boscoverysat/bsat.sat.electronica_de_abordo/pcb/receptor_rf_430mhz/pdf/Receptor RF - SCH.pdf

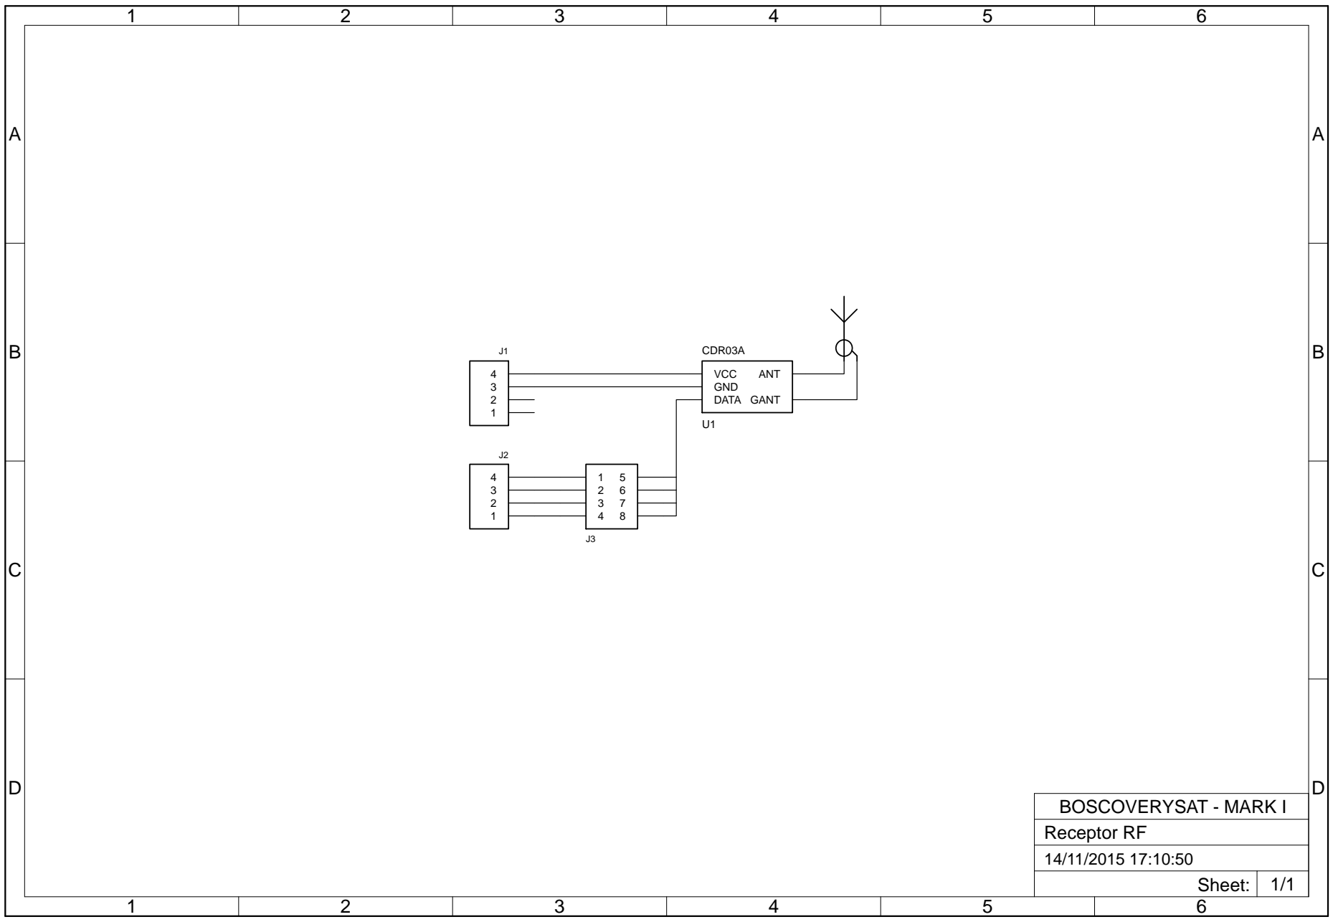
[picture p2: figure]
CDR03A; VCC; DATA; GND; ANT; GANT; Receptor RF; Sheet: 1/1; BOSCOVERYSAT - MARK I
