boscoverysat/bsat.sat.electronica_de_abordo/pcb/receptor_rf_430mhz/pdf/Receptor RF - PCB.pdf

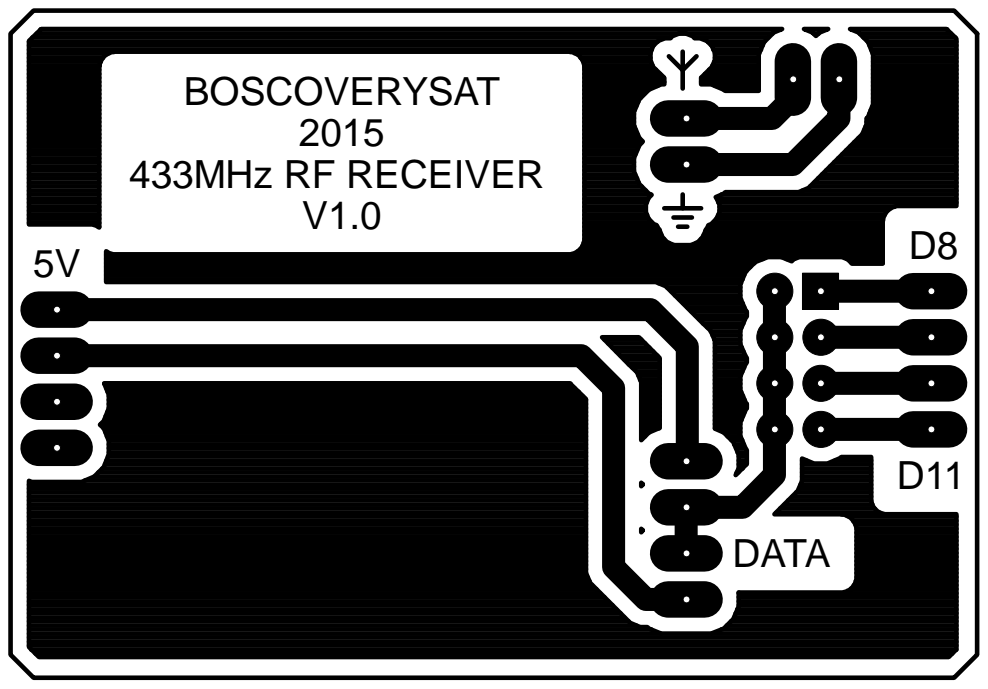
[picture p10: page 1]
BOSCOVERYSAT 2015 433MHz RF RECEIVER V1.0; DATA
