boscoverysat/bsat.sat.electronica_de_abordo/pcb/sat_control_shield/pdf/Sat Control Shield - PCB.pdf

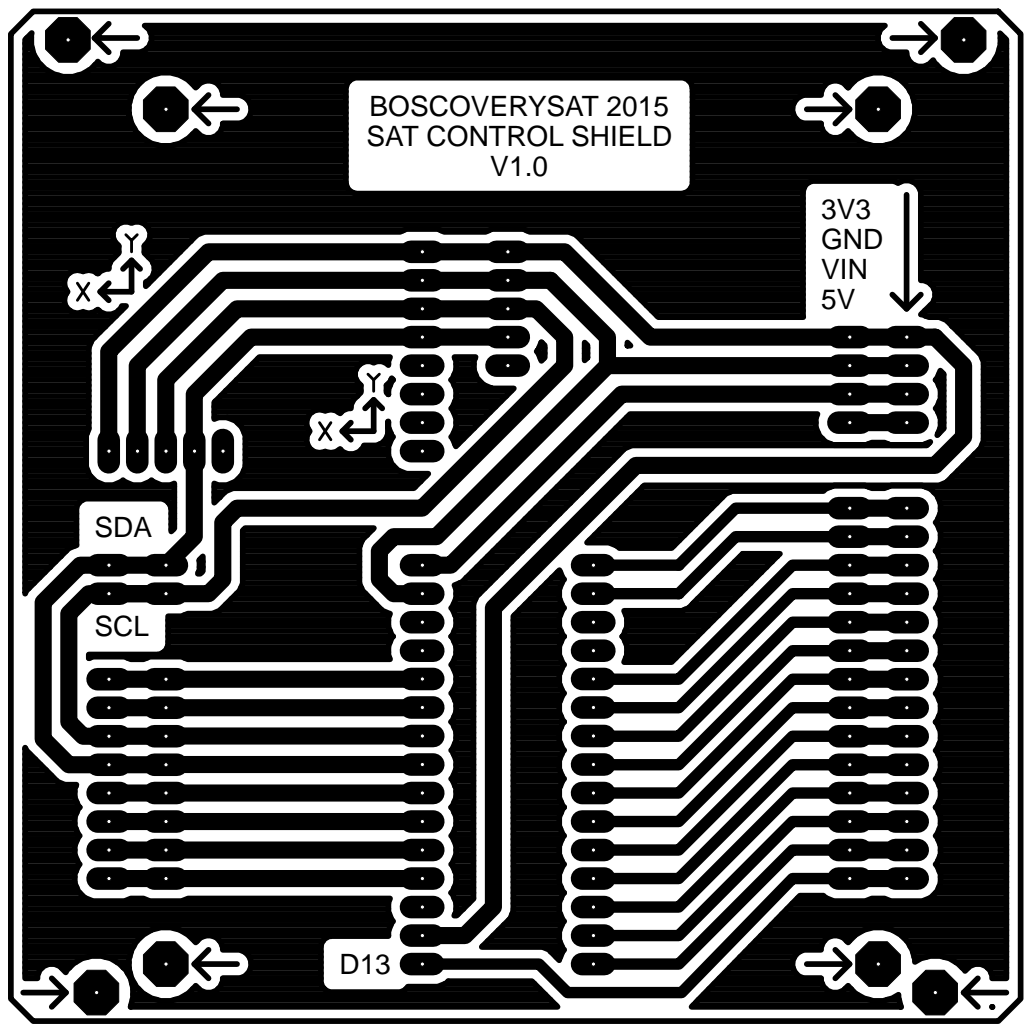
[picture p11: page 1]
SDA; SCL; 3V3 GND VIN 5V

BOSCOVERYSAT 2015
SAT CONTROL SHIELD
