boscoverysat/bsat.sat.electronica_de_abordo/pcb/sat_battery_shield/pdf/Sat Battery Shield - PCB.pdf

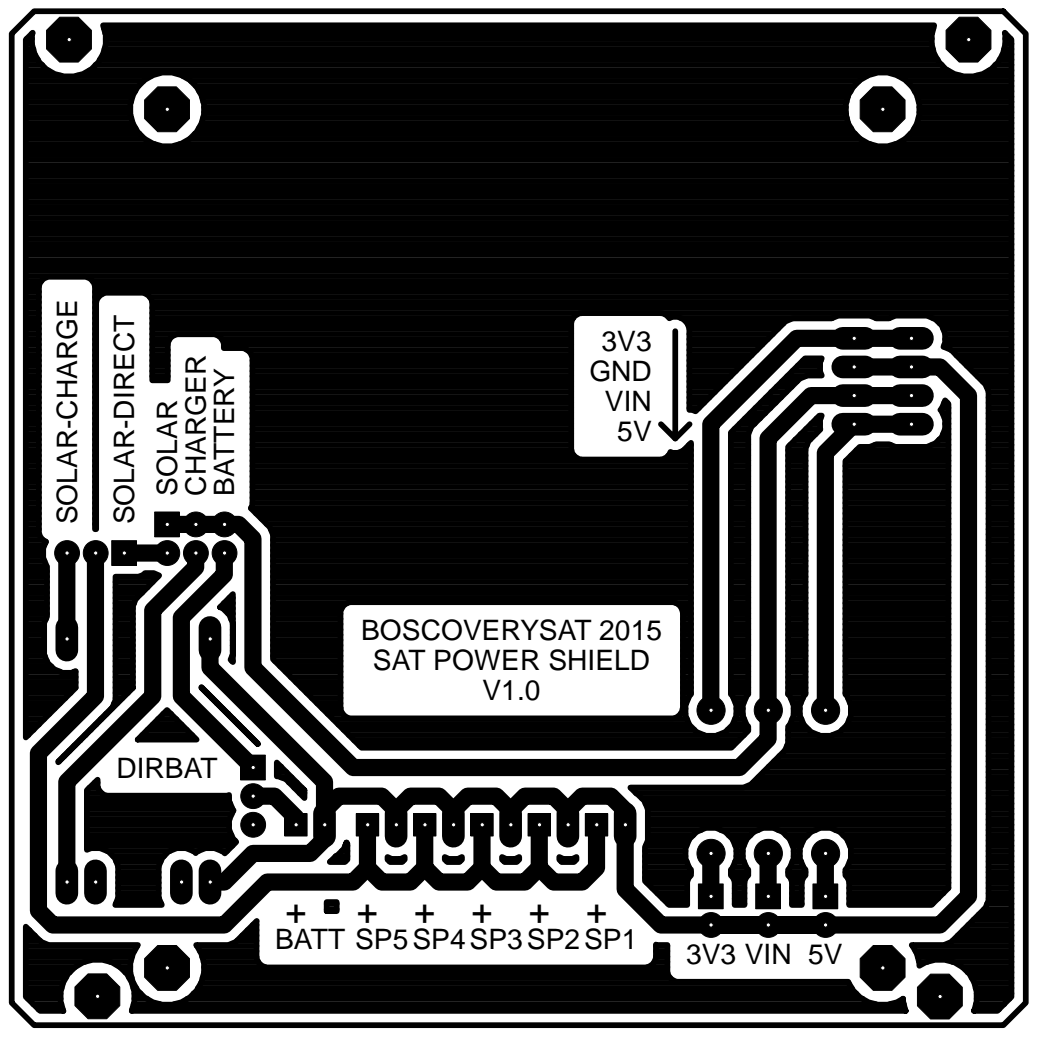
[picture p12: page 1]
BATT SP5SP4SP3SP2SP1; 3V3 VIN 5V; DIRBAT; SOLAR-CHARGE; SOLAR-DIRECT; SOLAR; CHARGER BATTERY; 3V3 GND VIN 5V

BOSCOVERYSAT 2015
SAT POWER SHIELD
