boscoverysat/bsat.sat.electronica_de_abordo/pcb/sat_battery_shield/pdf/Sat Battery Shield - SCH.pdf

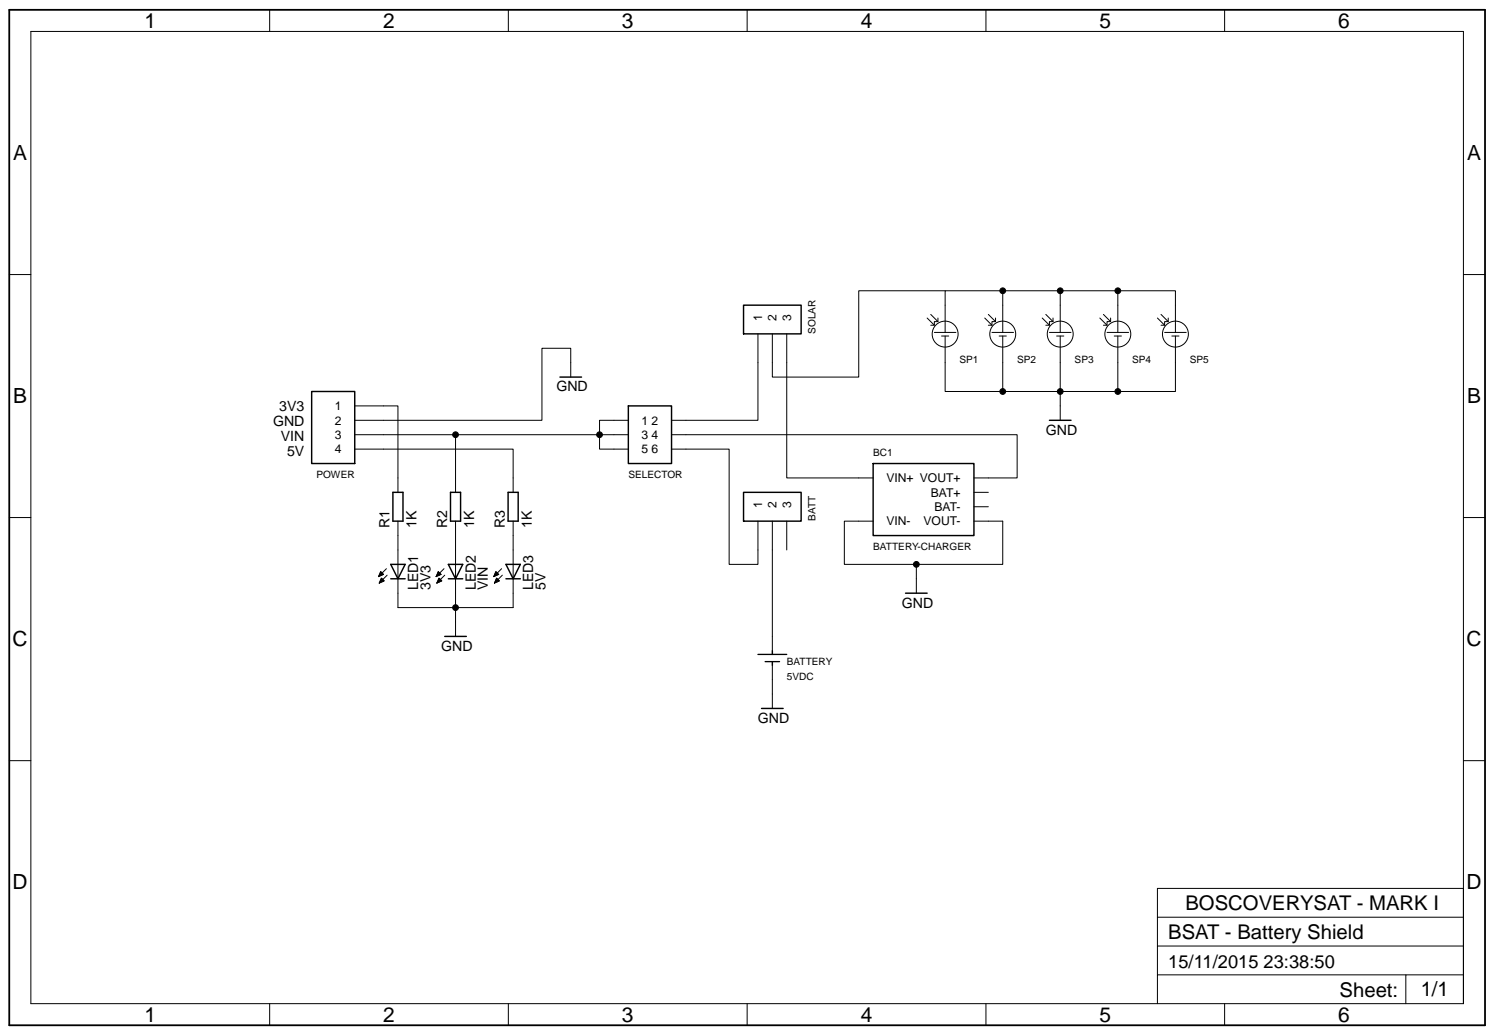
[picture p13: page 1]
3V3 GND VIN 5V; BATTERY-CHARGER; BATTERY; GND; VIN; POWER; SELECTOR; VIN+ VOUT+; BAT+ BAT- VIN- VOUT-; BATT; 5VDC; LED1; LED2; LED3; SOLAR; Sheet: 1/1

BOSCOVERYSAT - MARK I
BSAT - Battery Shield
